SamarthMaheshwari/Nirikshak-IIoT-Predictive-Maintenance/3D_Encloser/Images/1.png

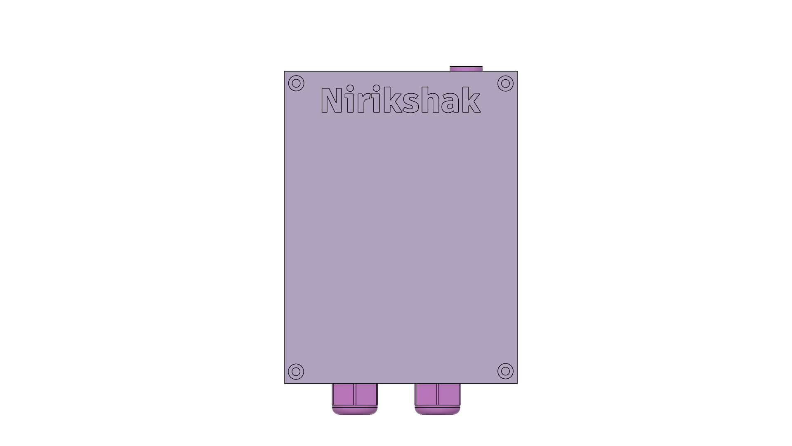
3D_Encloser/Images/1.png
