SamarthMaheshwari/Nirikshak-IIoT-Predictive-Maintenance/3D_Encloser/Images/2.png

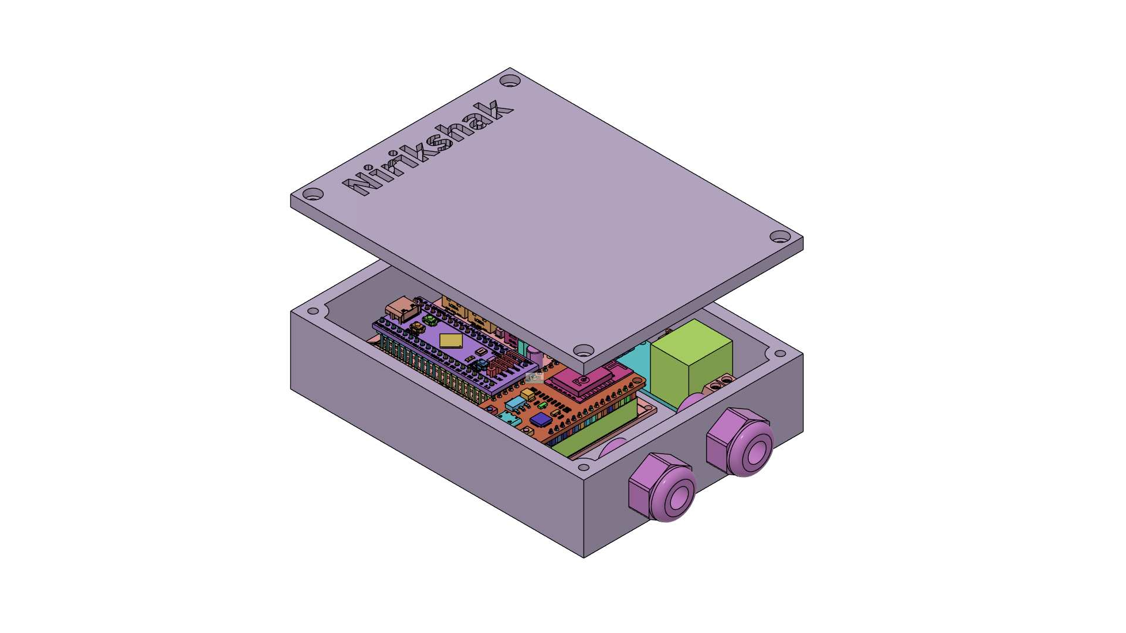
3D_Encloser/Images/2.png
