SamarthMaheshwari/Nirikshak-IIoT-Predictive-Maintenance/3D_Encloser/Images/3.png

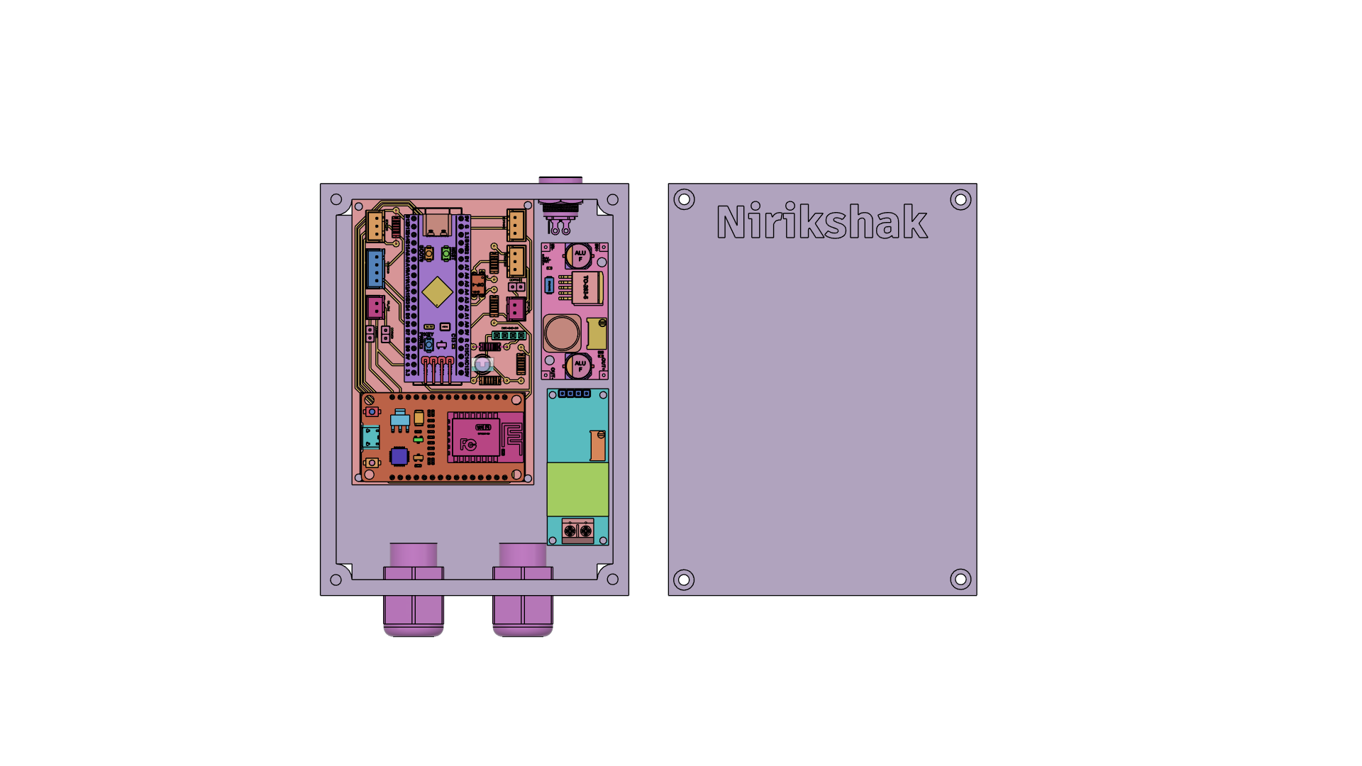
3D_Encloser/Images/3.png
