SamarthMaheshwari/Nirikshak-IIoT-Predictive-Maintenance/3D_Encloser/Images/4.png

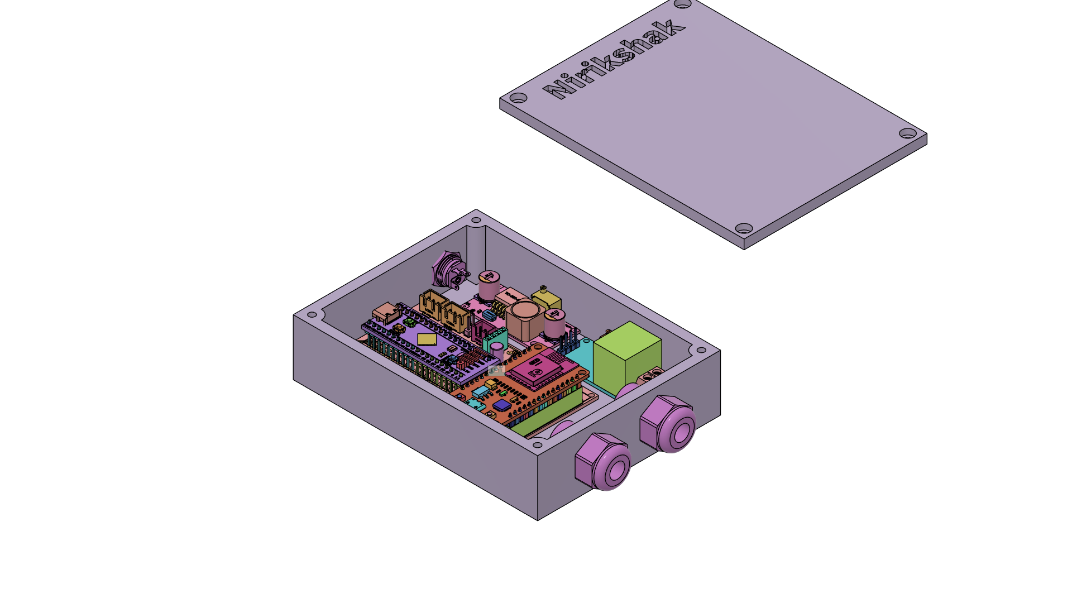
3D_Encloser/Images/4.png
